MTU-Autobot/interface-board/systems-controller/src/serial.h

/*
 * serial.h
 * function prototypes for serial
 */

#ifndef SERIAL_H_
#define SERIAL_H_

#define ENCODER_MSG 0xA0
#define DRIVE_MSG 0xA4

void serialPrint(const char * str);
uint16_t serialRead(char * buffer, uint16_t size, char stopChar);

#endif
